AESilky/sd-pgmr/sw/pico/src/app/deviceops/include/prog_device.h

/**
 * Programmable Device operations.
 *
 * Maintains the image to be programmed and provides operations to load/modify/save it and
 * perform operations on the device to be programmed.
 *
 * Copyright 2023-25 AESilky
 * SPDX-License-Identifier: MIT License
 *
*/
#ifndef PROG_DEVICE_H_
#define PROG_DEVICE_H_
#ifdef __cplusplus
extern "C" {
#endif

#include <stdbool.h>
#include <stdint.h>

/**
 * @brief Invalid Address indicator.
 * @ingroup device
 */
#define PD_INVALID_ADDR (0xFFFFFFFF)

/**
 * @brief Invalid Sector indicator.
 * @ingroup device
 */
#define PD_INVALID_SECT (0xFF)

/**
 * @brief Status of Programmable Device Operations.
 * @ingroup device
 */
typedef enum pd_op_status_ {
    PD_OP_OK = 0,
    PD_OP_CANCELLED,    // Cancelled (by request)
    PD_DEV_NOSUP,       // Device not supported
    PD_ERASE_FAIL,
    PD_FILE_OP_ERR,
    PD_NO_DEVICE,
    PD_DEVICE_SIZE,
    PD_NOT_READY,
    PD_NOT_IDENTIFIED,
    PD_NOT_ERASED,
    PD_ADDR_INVALID,
    PD_PROG_FAILED,
    PD_READ_FAILED,
    PD_VERIFY_FAILED,
} pd_op_status_t;

/**
 * @brief Information about a programmable device.
 * @ingroup device
 */
typedef struct mfg_device_info_s_ {
    uint8_t mfgid;      // Manufacturer ID
    uint8_t devid;      // Device ID
    uint8_t sectcnt;   // Sector Count (ie. 512K device with 64K sectors = 8)
    uint8_t abm;       // Address Bit Max (ie. 16 for a 128K device)
    const char* mfgs;   // Manufacturer Name (string)
    const char* devs;   // Device Name (string)
} md_info_t;

typedef enum pd_status_type_ {
    PDS_FILETYPE_BIN = 1,
    PDS_FILETYPE_HEX,
    PDS_PROC_HEX_REC,
    PDS_PROC_HEX_CMPT,
    PDS_PROC_BYTE,
    PDS_NOT_ERASED,
    PDS_DATA_MISMATCH,
    PDS_COMPLETED,
} pd_status_type;

/**
 * @brief Function prototype for a progress status handler.
 * @ingroup device
 *
 * @param x A status value. What it is depends on what is providing the status.
 * @param y A status value. What it is depends on what is providing the status.
 * @param z A status value. What it is depends on what is providing the status.
 *
 * @return Non-Zero to signal that the operation should be cancelled (if possible)
 */
typedef bool (*progstat_handler_fn)(pd_status_type stat, uint32_t x, uint32_t y, uint32_t z);


// //////////////////////////////////////////////////////////////////////////
// /// Inline Function forward declarations
// //////////////////////////////////////////////////////////////////////////

static inline uint32_t pd_sectsize(const md_info_t* info);


// //////////////////////////////////////////////////////////////////////////
// /// Regular Function declarations
// //////////////////////////////////////////////////////////////////////////

/**
 * @brief The maximum valid address for the device.
 * @ingroup device
 *
 * @param info md_info pointer for the device.
 * @return uint32_t
 */
static inline uint32_t pd_addrmax(const md_info_t* info) {
    return ((1 << (info->abm + 1)) - 1);
}

/**
 * @brief Erase device.
 * @ingroup device
 *
 * @param info md_info pointer for the device.
 * @return pd_op_status_t Operation status
 */
extern pd_op_status_t pd_erase_device(const md_info_t* info);

/**
 * @brief Erase sector.
 * @ingroup device
 *
 * @param info md_info pointer for the device.
 * @param sect The sector number (0 - (sectcnt - 1))
 * @return pd_op_status_t Operation status
 */
extern pd_op_status_t pd_erase_sect(const md_info_t* info, uint8_t sect);

/**
 * @brief Get the info for the current programmable device.
 * @ingroup device
 *
 * @return const md_info_t*
 */
extern const md_info_t* pd_info();

/**
 * @brief Check that the programmable device is empty (can be programmed).
 * @ingroup device
 *
 * Calls a progress status function after each 1K checked.
 *
 * @param Progress status handler function to be called (or NULL).
 * @return true The device is empty and can be programmed.
 * @return false The device isn't empty, or is unknown - and therefore, can't be programmed.
 */
extern bool pd_is_empty(const progstat_handler_fn progstatfn);

/**
 * @brief Check that the programmable device sector is empty (can be programmed).
 * @ingroup device
 *
 * @param sectno The 0-based sector to check
 * @param progstatfn Progress status function, or NULL.
 * @return true The sector is empty and can be programmed.
 * @return false The sector isn't empty, or the device isn't known.
 */
extern bool pd_is_sect_empty(uint8_t sectno, const progstat_handler_fn progstatfn);

/**
 * @brief The status of the last Programmable Device method.
 * @ingroup device
 *
 * Can be used to get the method status of the last method call for methods that
 * are not able to return a status.
 *
 * @return pd_op_status_t Status of the last operation
 */
extern pd_op_status_t pd_method_status();

/**
 * @brief Program the device from a binary file.
 * @ingroup device
 *
 * This performs a few tests:
 *  1) Can the file be stat'ed
 *  2) Is the file no larger than the device
 *  3) Can the file be opened for reading
 *
 * If those tests pass, the device will attempt to be programmed. At each 1K the
 * progress status function will be called with the address at that point.
 *
 * If, at any point, the value can't be programmed, the method will close the file and exit.
 *
 * @param info md_info pointer for the device.
 * @param filename Filename of the file to use.
 * @param progstatfn Progress status function, or NULL.
 * @return pd_op_status_t
 */
extern pd_op_status_t pd_prog_file(const md_info_t* info, const char* filename, const progstat_handler_fn progstatfn);

/**
 * @brief Read the device into a binary file.
 * @ingroup device
 *
 * This performs a check to see if the file can be created or truncated.
 *
 * @param info md_info pointer for the device.
 * @param filename Filename of the file to use.
 * @param progstatfn Progress status function, or NULL.
 * @return pd_op_status_t
 */
extern pd_op_status_t pd_read_to_fb(const md_info_t* info, const char* filename, const progstat_handler_fn progstatfn);

/**
 * @brief Read a value from a location of the device.
 * @ingroup device
 *
 * @param info md_info pointer for the device.
 * @param addr absolute address to read from
 * @return uint8_t value read
 */
extern uint8_t pd_read_value(const md_info_t* info, uint32_t addr);

/**
 * @brief Get the sector for an address within the address.
 * @ingroup device
 *
 * @param info md_info pointer for the device.
 * @return uint8_t The sector containing the address or PD_INVALID_SECT.
 */
static inline uint8_t pd_sect_for_addr(const md_info_t* info, uint32_t addr) {
    uint8_t sect = addr / pd_sectsize(info);
    return (sect < info->sectcnt ? sect : PD_INVALID_SECT);
}

/**
 * @brief Get the size of the sectors for the programmable device from the info.
 * @ingroup device
 *
 * @param info md_info pointer for the device.
 * @return uint32_t The size of the device in bytes.
 */
static inline uint32_t pd_sectsize(const md_info_t* info) {
    return((1 << (info->abm + 1)) / info->sectcnt);
}

/**
 * @brief Get the starting address of a sector (by sector number).
 * @ingroup device
 *
 * @param info md_info pointer for the device.
 * @param sect The sector number (0 - (sectcnt - 1))
 * @return uint32_t Start address of the sector or PD_INVALID_ADDR
 */
extern uint32_t pd_sectstart(const md_info_t* info, uint8_t sect);

/**
 * @brief Get the size of the programmable device from the info.
 * @ingroup device
 *
 * @param info md_info pointer for the device.
 * @return uint32_t The size of the device in bytes.
 */
static inline uint32_t pd_size(const md_info_t* info) {
    return(1 << (info->abm + 1));
}

/**
 * @brief Verify the device against a binary file.
 * @ingroup device
 *
 * This performs a few tests:
 *  1) Can the file be stat'ed
 *  2) Can the file be opened for reading
 *
 * If those tests pass, the device will be verified byte-by-byte. At each 1K the
 * progress status function will be called with the address at that point.
 *
 * If, at any point, the value doesn't match, the method will close the file and exit.
 *
 * @param info md_info pointer for the device.
 * @param filename Filename of the file to use.
 * @param lastaddr Pointer to a uint32_t to receive the address in error.
 * @param progstatfn Progress status function, or NULL.
 * @return pd_op_status_t
 */
extern pd_op_status_t pd_verify_fb(const md_info_t* info, const char* filename, uint32_t* lastaddr, const progstat_handler_fn progstatfn);

/**
 * @brief Write a value to a location of the device.
 * @ingroup device
 *
 * @param info md_info pointer for the device.
 * @param addr The address to write to. Must be within the capacity of the device.
 * @param value The value to write
 * @return pd_op_status_t
 */
extern pd_op_status_t pd_write_value(const md_info_t* info, uint32_t addr, uint8_t value);

/**
 * @brief Initialize the module. Must be called once/only-once before module use.
 * @ingroup device
 *
 */
extern void pd_modinit();

#ifdef __cplusplus
}
#endif
#endif // PROG_DEVICE_H_
