AESilky/sd-pgmr/sw/pico/src/dbus/cmd/cmds.h

/**
 * Shell Commands: Data Bus Operations
 *
 * Command to set the Data Bus as In/Out, see if it is In/Out, Write/Read it.
 *
 * Copyright 2023-25 AESilky
 * SPDX-License-Identifier: MIT License
 *
*/
#ifndef CMDS_DBUS_H_
#define CMDS_DBUS_H_
#ifdef __cplusplus
extern "C" {
#endif

extern void dbuscmds_modinit(void);

#ifdef __cplusplus
}
#endif
#endif // CMDS_DBUS_H_
